antonjan/sig_scan/1000016056.jpg

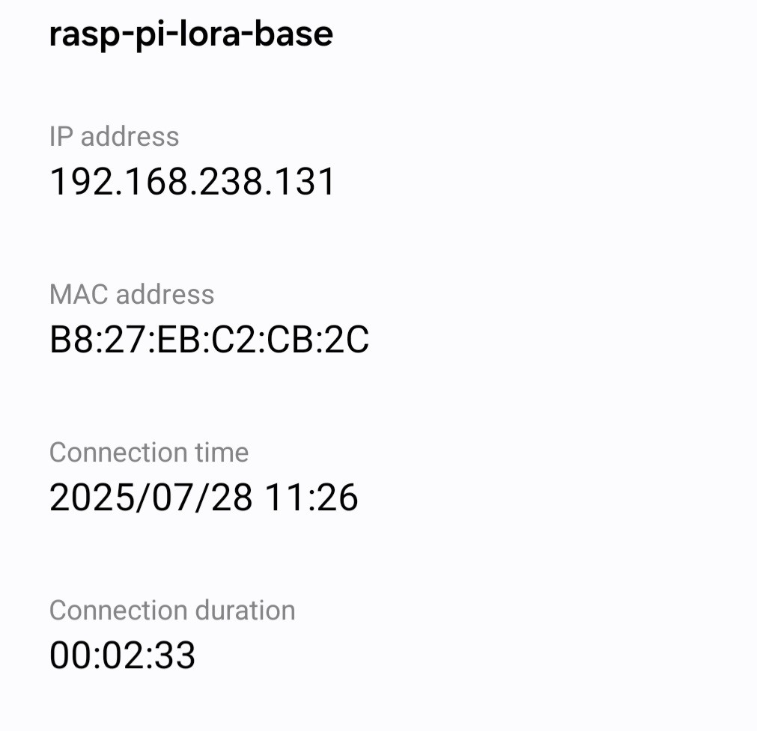
1000016056.jpg
