antonjan/sig_scan/Pi_Code_File/LoRa_communication_Tests/LoRa_Receiver_Test_V1.py

#!/usr/bin/env python3
# -*- coding: utf-8 -*-

#
# SPDX-License-Identifier: GPL-3.0
#
# GNU Radio Python Flow Graph
# Title: Not titled yet
# GNU Radio version: 3.10.9.2

from PyQt5 import Qt
from gnuradio import qtgui
from gnuradio import blocks
import pmt
from gnuradio import blocks, gr
from gnuradio import gr
from gnuradio.filter import firdes
from gnuradio.fft import window
import sys
import signal
from PyQt5 import Qt
from argparse import ArgumentParser
from gnuradio.eng_arg import eng_float, intx
from gnuradio import eng_notation
import lora
import osmosdr
import time
import sip



class LoRa_Receiver_Test_V1(gr.top_block, Qt.QWidget):

    def __init__(self):
        gr.top_block.__init__(self, "Not titled yet", catch_exceptions=True)
        Qt.QWidget.__init__(self)
        self.setWindowTitle("Not titled yet")
        qtgui.util.check_set_qss()
        try:
            self.setWindowIcon(Qt.QIcon.fromTheme('gnuradio-grc'))
        except BaseException as exc:
            print(f"Qt GUI: Could not set Icon: {str(exc)}", file=sys.stderr)
        self.top_scroll_layout = Qt.QVBoxLayout()
        self.setLayout(self.top_scroll_layout)
        self.top_scroll = Qt.QScrollArea()
        self.top_scroll.setFrameStyle(Qt.QFrame.NoFrame)
        self.top_scroll_layout.addWidget(self.top_scroll)
        self.top_scroll.setWidgetResizable(True)
        self.top_widget = Qt.QWidget()
        self.top_scroll.setWidget(self.top_widget)
        self.top_layout = Qt.QVBoxLayout(self.top_widget)
        self.top_grid_layout = Qt.QGridLayout()
        self.top_layout.addLayout(self.top_grid_layout)

        self.settings = Qt.QSettings("GNU Radio", "LoRa_Receiver_Test_V1")

        try:
            geometry = self.settings.value("geometry")
            if geometry:
                self.restoreGeometry(geometry)
        except BaseException as exc:
            print(f"Qt GUI: Could not restore geometry: {str(exc)}", file=sys.stderr)

        ##################################################
        # Blocks
        ##################################################

        self.rtlsdr_source_0 = osmosdr.source(
            args="numchan=" + str(1) + " " + ""
        )
        self.rtlsdr_source_0.set_time_unknown_pps(osmosdr.time_spec_t())
        self.rtlsdr_source_0.set_sample_rate(1e6)
        self.rtlsdr_source_0.set_center_freq(868e6, 0)
        self.rtlsdr_source_0.set_freq_corr(0, 0)
        self.rtlsdr_source_0.set_dc_offset_mode(0, 0)
        self.rtlsdr_source_0.set_iq_balance_mode(0, 0)
        self.rtlsdr_source_0.set_gain_mode(False, 0)
        self.rtlsdr_source_0.set_gain(10, 0)
        self.rtlsdr_source_0.set_if_gain(20, 0)
        self.rtlsdr_source_0.set_bb_gain(20, 0)
        self.rtlsdr_source_0.set_antenna('', 0)
        self.rtlsdr_source_0.set_bandwidth(0, 0)
        self.qtgui_freq_sink_x_0 = qtgui.freq_sink_c(
            1024, #size
            window.WIN_BLACKMAN_hARRIS, #wintype
            0, #fc
            1e6, #bw
            "", #name
            1,
            None # parent
        )
        self.qtgui_freq_sink_x_0.set_update_time(0.10)
        self.qtgui_freq_sink_x_0.set_y_axis((-140), 10)
        self.qtgui_freq_sink_x_0.set_y_label('Relative Gain', 'dB')
        self.qtgui_freq_sink_x_0.set_trigger_mode(qtgui.TRIG_MODE_FREE, 0.0, 0, "")
        self.qtgui_freq_sink_x_0.enable_autoscale(False)
        self.qtgui_freq_sink_x_0.enable_grid(False)
        self.qtgui_freq_sink_x_0.set_fft_average(1.0)
        self.qtgui_freq_sink_x_0.enable_axis_labels(True)
        self.qtgui_freq_sink_x_0.enable_control_panel(False)
        self.qtgui_freq_sink_x_0.set_fft_window_normalized(False)



        labels = ['', '', '', '', '',
            '', '', '', '', '']
        widths = [1, 1, 1, 1, 1,
            1, 1, 1, 1, 1]
        colors = ["blue", "red", "green", "black", "cyan",
            "magenta", "yellow", "dark red", "dark green", "dark blue"]
        alphas = [1.0, 1.0, 1.0, 1.0, 1.0,
            1.0, 1.0, 1.0, 1.0, 1.0]

        for i in range(1):
            if len(labels[i]) == 0:
                self.qtgui_freq_sink_x_0.set_line_label(i, "Data {0}".format(i))
            else:
                self.qtgui_freq_sink_x_0.set_line_label(i, labels[i])
            self.qtgui_freq_sink_x_0.set_line_width(i, widths[i])
            self.qtgui_freq_sink_x_0.set_line_color(i, colors[i])
            self.qtgui_freq_sink_x_0.set_line_alpha(i, alphas[i])

        self._qtgui_freq_sink_x_0_win = sip.wrapinstance(self.qtgui_freq_sink_x_0.qwidget(), Qt.QWidget)
        self.top_layout.addWidget(self._qtgui_freq_sink_x_0_win)
        self.lora_message_socket_sink_0 = lora.message_socket_sink('127.0.0.1', 40868, 0)
        self.lora_message_file_sink_0 = lora.message_file_sink('/home/jacques/desktop/LoRa.log')
        self.lora_lora_receiver_0 = lora.lora_receiver(1e6, 868e6, [868e6], 125000, 7, False, 4, True, False, False, 1, False, False)
        self.blocks_message_strobe_0 = blocks.message_strobe(pmt.intern("TEST"), 1000)
        self.blocks_message_debug_0 = blocks.message_debug(True, gr.log_levels.info)


        ##################################################
        # Connections
        ##################################################
        self.msg_connect((self.blocks_message_strobe_0, 'strobe'), (self.blocks_message_debug_0, 'print'))
        self.msg_connect((self.lora_lora_receiver_0, 'frames'), (self.blocks_message_strobe_0, 'set_msg'))
        self.msg_connect((self.lora_lora_receiver_0, 'frames'), (self.lora_message_file_sink_0, 'in'))
        self.msg_connect((self.lora_lora_receiver_0, 'frames'), (self.lora_message_socket_sink_0, 'in'))
        self.connect((self.rtlsdr_source_0, 0), (self.lora_lora_receiver_0, 0))
        self.connect((self.rtlsdr_source_0, 0), (self.qtgui_freq_sink_x_0, 0))


    def closeEvent(self, event):
        self.settings = Qt.QSettings("GNU Radio", "LoRa_Receiver_Test_V1")
        self.settings.setValue("geometry", self.saveGeometry())
        self.stop()
        self.wait()

        event.accept()




def main(top_block_cls=LoRa_Receiver_Test_V1, options=None):

    qapp = Qt.QApplication(sys.argv)

    tb = top_block_cls()

    tb.start()

    tb.show()

    def sig_handler(sig=None, frame=None):
        tb.stop()
        tb.wait()

        Qt.QApplication.quit()

    signal.signal(signal.SIGINT, sig_handler)
    signal.signal(signal.SIGTERM, sig_handler)

    timer = Qt.QTimer()
    timer.start(500)
    timer.timeout.connect(lambda: None)

    qapp.exec_()

if __name__ == '__main__':
    main()
